mausi-mick/AD9833-Simple-Function-Generator-/P1000196.JPG

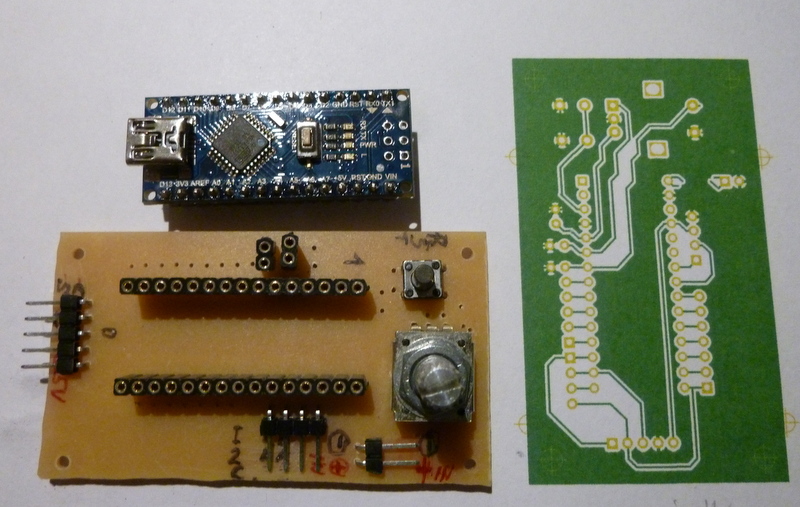
P1000196.JPG
